hedfd434/custom_eval_stm32L43KCU6/images/IMG_2161.jpeg

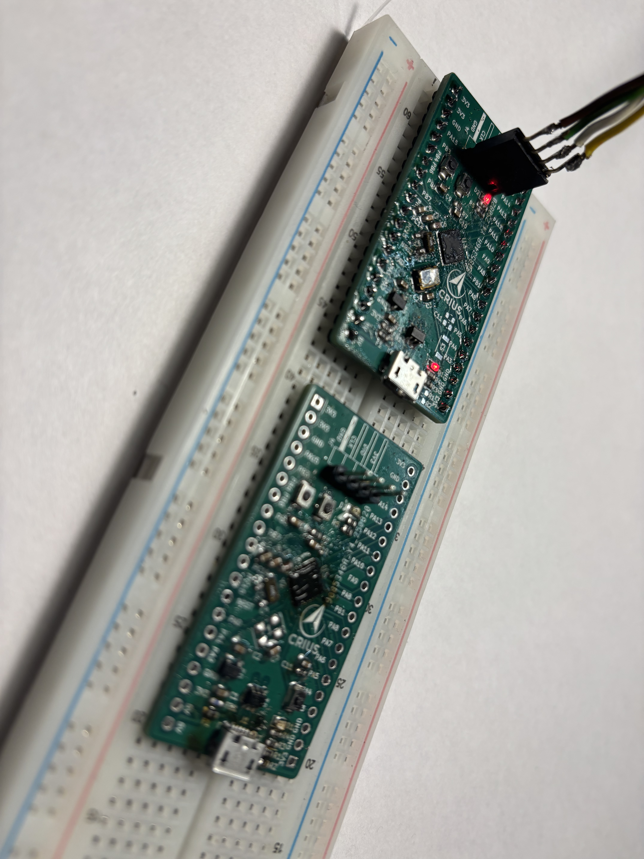
images/IMG_2161.jpeg
